PKI-IEEE/Laser_Harp/AVR_Studio_6_Project/LaserHarp/music.c

// Author: Josh Hansen
// Pre-programmed Music by Brain Felderman
// Date: Oct 2015

#define F_CPU 16000000 // 16 MHz clock freq 
#include <util/delay.h>
#include <avr/io.h>
#include "music.h"
#include "LaserHarp.h"

// C4 8-bit Piano waveform (takes 10k of program mem)
const uint8_t pianoWaveform[10000] PROGMEM =
{
	118,128,118,108,118,128,138,138,118,148,88,108,128,88,108,108,118,78,108,118,108,78,98,158,128,138,138,148,138,128,158,148,148,138,128,128,118,128,128,158,88,168,178,118,148,128,138,118,148,128,138,118,108,118,88,48,58,68,48,38,38,78,68,8,78,128,128,148,108,128,98,118,148,148,138,128,118,158,148,118,168,148,148,198,188,148,208,148,158,168,178,158,158,138,138,158,98,88,58,108,
	68,58,58,78,68,38,98,128,138,148,138,138,108,118,138,148,138,88,118,128,138,98,158,148,138,188,148,168,168,168,138,178,158,168,168,128,138,128,98,78,58,78,48,38,38,68,48,38,118,138,158,138,168,148,128,118,138,138,118,88,78,138,98,98,138,128,128,178,128,168,168,158,148,168,148,168,158,108,148,108,98,58,48,68,48,38,58,68,58,58,118,158,158,158,188,168,148,138,138,178,
	128,98,98,148,108,118,168,128,178,168,158,168,188,148,158,168,148,178,148,118,138,108,98,58,48,58,48,28,58,68,38,68,98,158,148,158,178,158,158,128,148,158,128,78,108,128,118,118,158,128,178,168,158,178,198,158,158,168,148,188,138,128,118,108,88,48,38,48,38,18,48,58,38,58,88,138,138,148,178,148,158,108,138,148,118,68,98,128,88,138,118,148,168,178,158,198,198,168,178,168,
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

		play32Note(F3);
		play32Note(Fs3);
		play32Note(G3);
		play32Note(Gs3);
		play32Note(A3);
		play32Note(B3);
		play32Note(C3);
		play32Note(Cs4);

		play32Note(D4);
		play32Note(Cs4);
		play32Note(C3);
		play32Note(B3);
		play32Note(As3);
		play32Note(Ds4);
		play32Note(D4);
		play32Note(Cs4);

		play32Note(D4);
		play32Note(Cs4);
		play32Note(C3);
		play32Note(B3);
		play32Note(As3);
		play32Note(B3);
		play32Note(C3);
		play32Note(Cs4);

		play32Note(D4);
		play32Note(Cs4);
		play32Note(C3);
		play32Note(B3);
		play32Note(As3);
		play32Note(Ds4);
		play32Note(D4);
		play32Note(Cs4);

		play32Note(D4);
		play32Note(Cs4);
		play32Note(C3);
		play32Note(B3);
		play32Note(As3);
		play32Note(B3);
		play32Note(C3);
		play32Note(Cs4);

		play32Note(D4);
		play32Note(Cs4);
		play32Note(C3);
		play32Note(B3);
		play32Note(C3);
		play32Note(B3);
		play32Note(As3);
		play32Note(A3);
		
	}

}
